sunaabh-trivedi/sf4-project/Datalogger_Circuits/Datalogger_Circuits.kicad_sch

## KiCad design Datalogger_Circuits/Datalogger_Circuits.kicad_sch (2024-05-28)

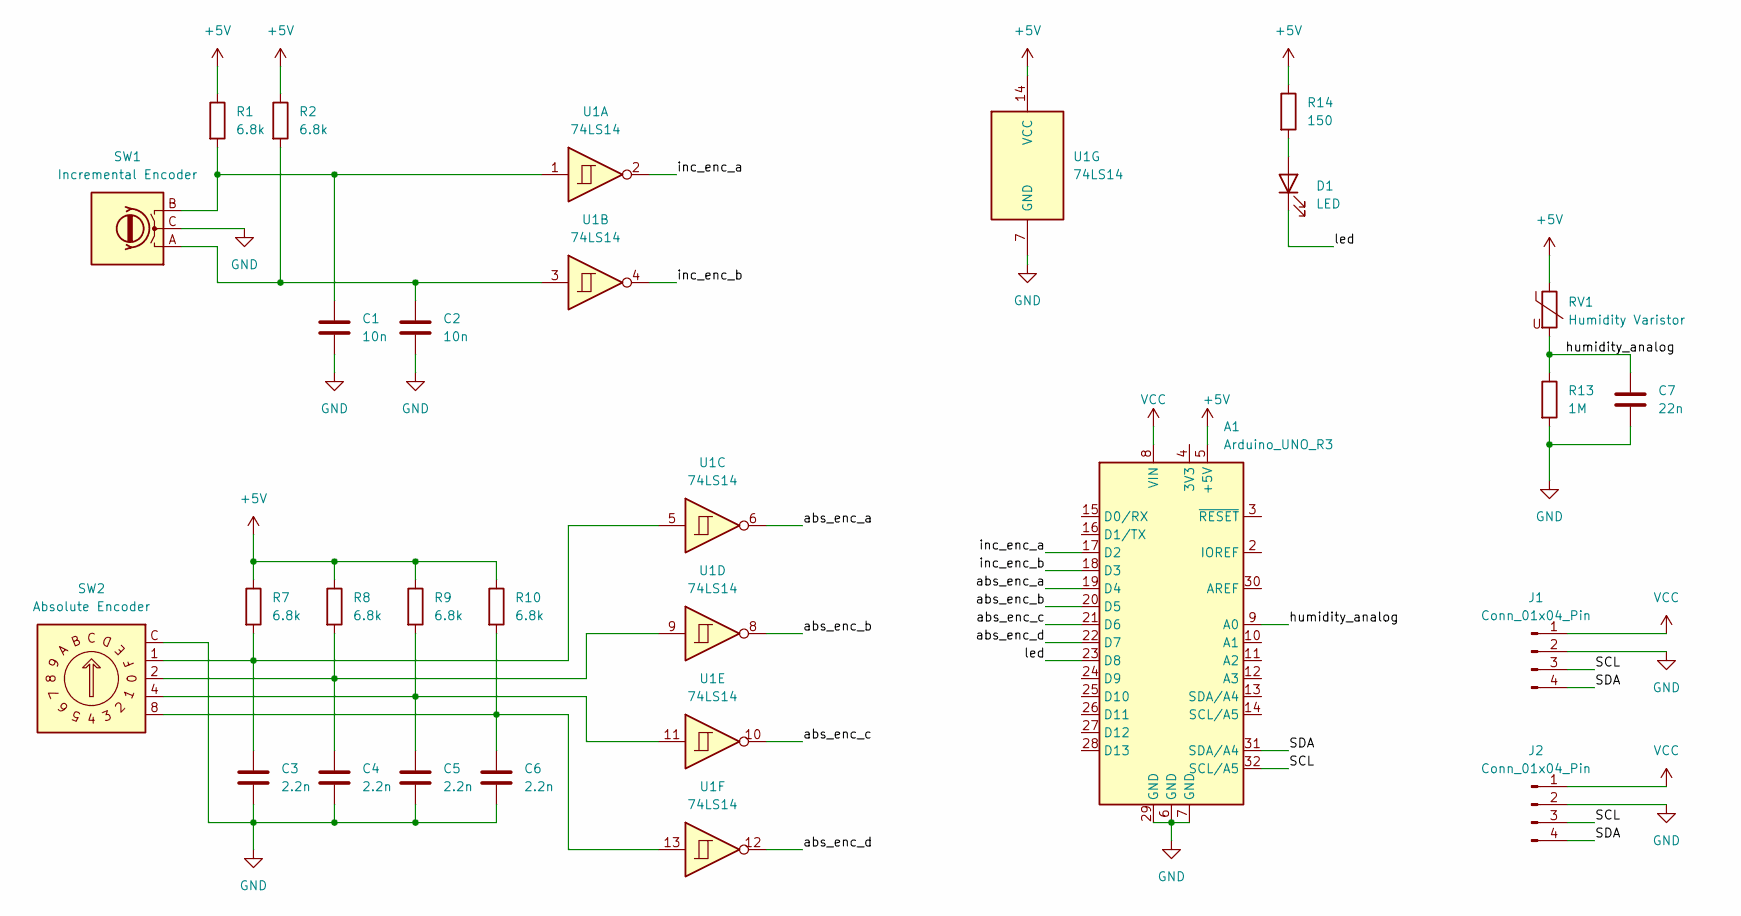
[picture p4: schematic Datalogger_Circuits.kicad_sch]

Parts:
A1: Arduino_UNO_R3
C1, C2: 10n
C3, C4, C5, C6: 2.2n
C7: 22n
D1: LED
J1, J2: Conn_01x04_Pin
R1, R2, R7, R8, R9, R10: 6.8k
R13: 1M
R14: 150
RV1: Humidity Varistor
SW1: Incremental Encoder
SW2: Absolute Encoder; Nidec_Copal_SH-7040B
U1: 74LS14

Connections:
+5V: A1.5 (+5V), R1.1, R2.1, R7.1, R8.1, R9.1, R10.1, R14.1, RV1.1, U1.14 (VCC)
GND: A1.6 (GND), A1.7 (GND), A1.29 (GND), C1.2, C2.2, C3.2, C4.2, C5.2, C6.2, C7.2, J1.2, J2.2, R13.2, SW1.C, SW2.C, U1.7 (GND)
unnamed: C1.1, R1.2, SW1.B, U1.1
unnamed: C2.1, R2.2, SW1.A, U1.3
unnamed: C3.1, R7.2, SW2.1, U1.5
unnamed: C4.1, R8.2, SW2.2, U1.9
unnamed: C5.1, R9.2, SW2.4, U1.11
unnamed: C6.1, R10.2, SW2.8, U1.13
unnamed: C7.1, R13.1, RV1.2
unnamed: D1.2 (A), R14.2
SCL: A1.32 (SCL/A5), J1.3, J2.3
SDA: A1.31 (SDA/A4), J1.4, J2.4
VCC: A1.8 (VIN), J1.1, J2.1
abs_enc_a: A1.19 (D4), U1.6
abs_enc_b: A1.20 (D5), U1.8
abs_enc_c: A1.21 (D6), U1.10
abs_enc_d: A1.22 (D7), U1.12
humidity_analog: A1.9 (A0)
inc_enc_a: A1.17 (D2), U1.2
inc_enc_b: A1.18 (D3), U1.4
led: A1.23 (D8), D1.1 (K)
